paclema/iot-postbox/src/PostBox.h

#ifndef PostBox_H
#define PostBox_H

#pragma once
#include <Arduino.h>

#ifdef ESP32
#include <esp_wifi.h>
#include <WiFi.h>

//Power Management and ADC sense inputs
// ------------------------------------
#include "PowerManagement.h"

#endif


#include <MQTTClient.h>


// WS2812B LED strip
// -----------------
#include <FastLED.h>

#ifdef ARDUINO_IOTPOSTBOX_V1
  #define LED_PIN    PIN_NEOPIXEL 	//GPIO17
#else
  #define LED_PIN    15 			//GPIO15
#endif

#define NUM_LEDS  4
#define BRIGHTNESS 10


// PostBoxSwitch sensors
// ---------------------
#include "PostBoxSwitch.h"
#ifndef ARDUINO_IOTPOSTBOX_V1
  #define SW1_PIN         12
  #define SW2_PIN         13
  #define KEEP_WAKE_PIN   14    // Pin which is used to Keep ESP awake until job is finished
#endif


// PostBox sleep configs
// ---------------------
#define WAKE_UP_BITMASK ( GPIO_NUM_4 | GPIO_NUM_5 )
RTC_DATA_ATTR static int bootCount = 0;


// Battery charger feedback
// ------------------------
#ifdef ARDUINO_IOTPOSTBOX_V1
//TODO: BATTERY, USB POWER AND CHARGING SENSE

#else
//Using tp4056 charger with battery fedback to ADC0 (max 1v! for ESP8266) and tp4056 chrg and stdby pins feedback:
  #define USE_TP4056
  #define NO_SLEEP_WHILE_CHARGING    // While charging the ESP won't go to sleep. Comment out this line if you want to avoid that

  #ifdef USE_TP4056
    #define CHRG_PIN    4    // Pin for charge battery. LOW when usb is connected and baterry is being charged.
    #define STDBY_PIN   5    // Pin for stdby battery charge. LOW for battery charge termination.
  #else
    ADC_MODE(ADC_VCC);          // Allows to monitor the internal VCC level; it varies with WiFi load
  #endif
#endif


class PostBox {
public:
	CRGB leds[NUM_LEDS];

	PostBoxSwitch sw1;
	PostBoxSwitch sw2;


	String MQTTBaseTopic;
	MQTTClient *mqtt;

	PowerManagement power;
	PowerStatus powerStatus = PowerStatus::Unknown;
	ChargingStatus chargingStatus = ChargingStatus::Unknown;


	PostBox(void);
	~PostBox(void);

	void setup(void);
	void init(void);
	void loop(void);
	void powerOff(void);

	void updatePowerStatus(void);

	float readVoltage(void);
	float getVBus(void) { return power.vBusSense.mV;};
	float getVBat(void) { return power.vBatSense.mV;};
	float getVBatNow(void) { return power.vBatSense.getLastmV(); };
	float getVBatStat(void) { return power.getVBatStat();};
	ChargingStatus getChargingStatus(void) { return chargingStatus;};
	PowerStatus getPowerStatus(void) { return powerStatus;};
	bool isWakeUpPublished(void) { return wakeUpPublished;};



	void updateLedStrip(void);

	void printWakeupReason(void);
	void setupDeepSleep(void);
	void turnOffDevice(void);

	void publishWakeUp(String topic_end);

	void setMQTTBaseTopic(String topic) { MQTTBaseTopic = topic; }
	void setMQTTClient(MQTTClient * client) { mqtt = client; }



private:

	bool wakeUpPublished = false;
	int wakeUpGPIO = -1;              // Variable to store the GPIO which triggered the wake from Deep Sleep


};

#endif
