paclema/iot-postbox/boards/variants/iotpostbox_v1_4mb/variant.cpp

/* 
 * The MIT License (MIT)
 *
 * Copyright (c) 2021 Ha Thach (tinyusb.org) for Adafruit Industries
 *
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
 * THE SOFTWARE IS PROVIDED "AS IS", WITHOUT WARRANTY OF ANY KIND, EXPRESS OR
 * IMPLIED, INCLUDING BUT NOT LIMITED TO THE WARRANTIES OF MERCHANTABILITY,
 * FITNESS FOR A PARTICULAR PURPOSE AND NONINFRINGEMENT. IN NO EVENT SHALL THE
 * AUTHORS OR COPYRIGHT HOLDERS BE LIABLE FOR ANY CLAIM, DAMAGES OR OTHER
 * LIABILITY, WHETHER IN AN ACTION OF CONTRACT, TORT OR OTHERWISE, ARISING FROM,
 * OUT OF OR IN CONNECTION WITH THE SOFTWARE OR THE USE OR OTHER DEALINGS IN
 * THE SOFTWARE.
 */


#include "esp32-hal-gpio.h"
#include "pins_arduino.h"

extern "C" {

// Initialize variant/board, called before setup()
void initVariant(void)
{
  // This board has a power control pin, and we must set it to output and high
  // in order to enable the NeoPixels.
  pinMode(NEOPIXEL_POWER, OUTPUT);
  digitalWrite(NEOPIXEL_POWER, HIGH);

  // turn on the I2C power by setting pin to opposite of 'rest state'
  // pinMode(PIN_I2C_POWER, INPUT);
  // delay(1);
  // bool polarity = digitalRead(PIN_I2C_POWER);
  // pinMode(PIN_I2C_POWER, OUTPUT);
  // digitalWrite(PIN_I2C_POWER, !polarity);
}
}
